mofosyne/openscad-rail-slot-mounts/screw/screw_mountable_smd_cut_tape_holder/png/screwMountableSMDcutTapeHolder.stl.png

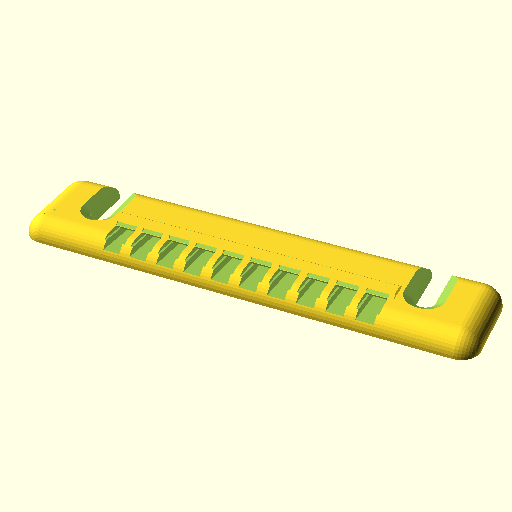
screw/screw_mountable_smd_cut_tape_holder/png/screwMountableSMDcutTapeHolder.stl.png
