mofosyne/openscad-rail-slot-mounts/screw/screw_mountable_wire_holder/png/screwMountableScrewdriverHolder.stl.png

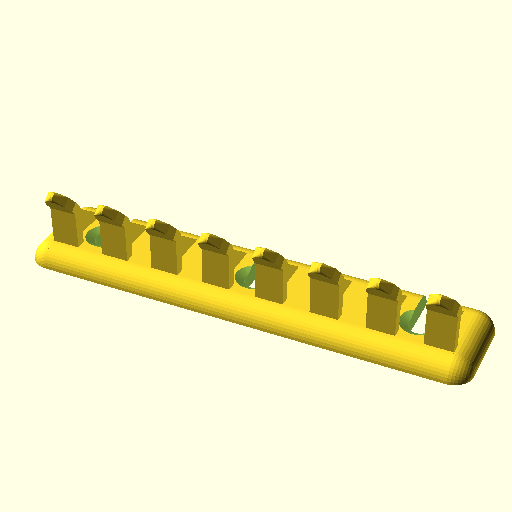
screw/screw_mountable_wire_holder/png/screwMountableScrewdriverHolder.stl.png
