mofosyne/openscad-rail-slot-mounts/screw/screw_mountable_wire_holder/png/screwMountableWireHolder.stl.png

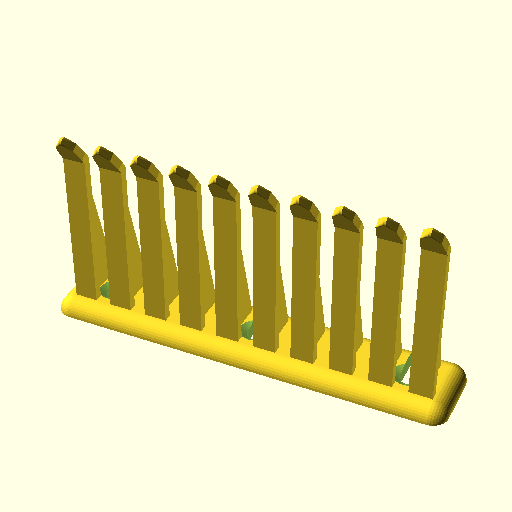
screw/screw_mountable_wire_holder/png/screwMountableWireHolder.stl.png
