mofosyne/openscad-rail-slot-mounts/tslot/png/tslot_cable_hook.stl.png

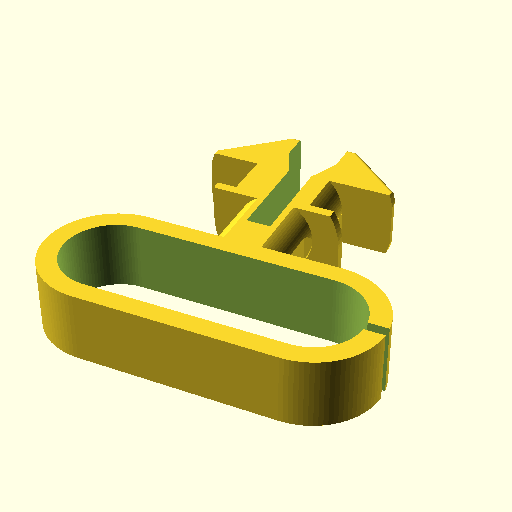
tslot/png/tslot_cable_hook.stl.png
