mofosyne/openscad-rail-slot-mounts/tslot/png/tslot_ethernet_cable_clip.stl.png

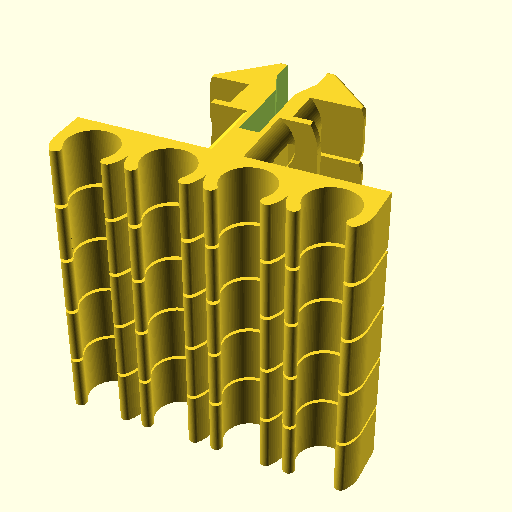
tslot/png/tslot_ethernet_cable_clip.stl.png
