mofosyne/openscad-rail-slot-mounts/tslot/png/tslot_screwdriver_mount.stl.png

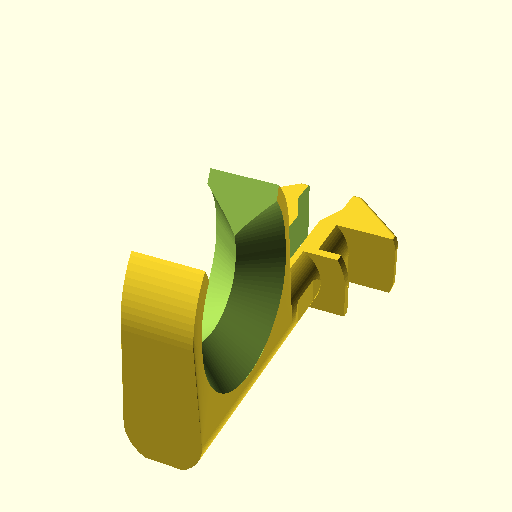
tslot/png/tslot_screwdriver_mount.stl.png
