mofosyne/openscad-rail-slot-mounts/tslot/png/tslot_tape_holderwCatch.stl.png

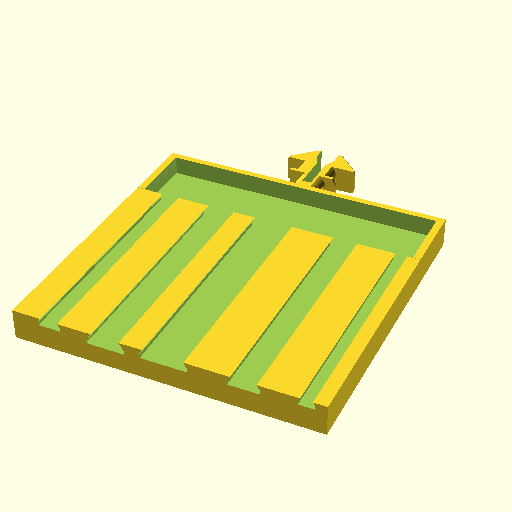
tslot/png/tslot_tape_holderwCatch.stl.png
