mofosyne/openscad-rail-slot-mounts/tslot/stl/tslot_pen_holder.stl

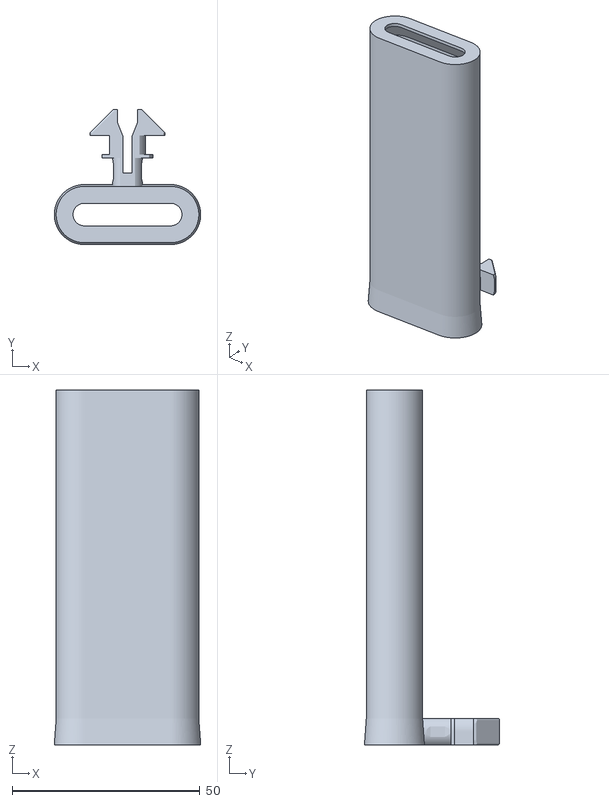
[picture p31: CAD file, 2024-09-13]
tslot/stl/tslot_pen_holder.stl
39.0 x 36.0 x 94.5
