mofosyne/openscad-rail-slot-mounts/tslot/stl/tslot.stl

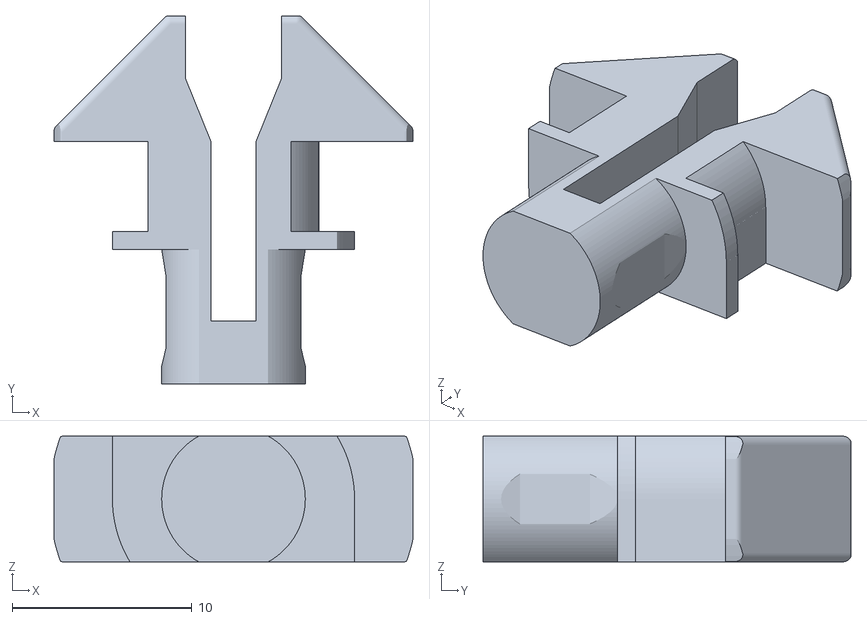
[picture p32: CAD file, 2024-09-13]
tslot/stl/tslot.stl
20.0 x 20.5 x 7.00
