mofosyne/openscad-rail-slot-mounts/tslot/stl/tslot_smd_feeder.stl

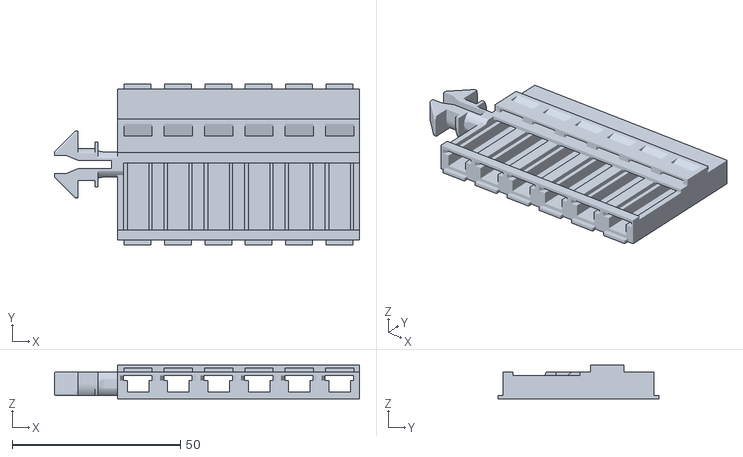
[picture p33: CAD file, 2024-09-13]
tslot/stl/tslot_smd_feeder.stl
90.8 x 48.0 x 10.0
