mofosyne/openscad-rail-slot-mounts/tslot/stl/tslot_cable_loop.stl

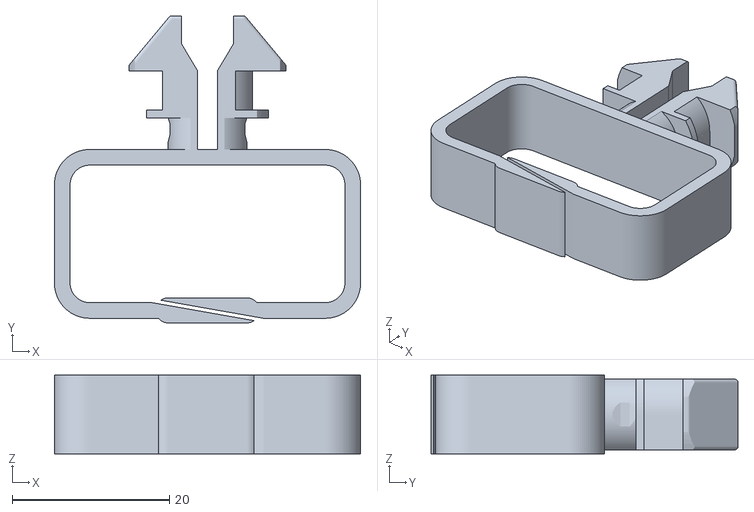
[picture p34: CAD file, 2024-09-13]
tslot/stl/tslot_cable_loop.stl
39.0 x 39.1 x 10.0
