mofosyne/openscad-rail-slot-mounts/tslot/stl/tslot_ethernet_cable_clip.stl

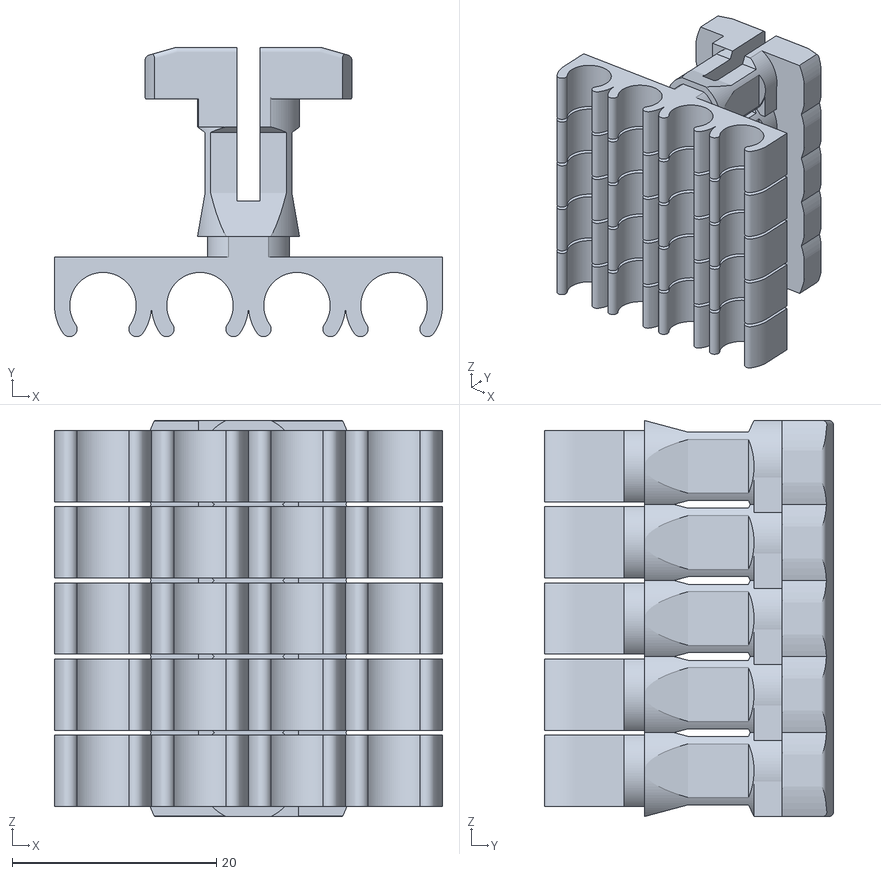
[picture p35: CAD file, 2024-09-08]
tslot/stl/tslot_ethernet_cable_clip.stl
38.0 x 28.3 x 38.8
