mofosyne/openscad-rail-slot-mounts/TRailExample.scad

rotate([90,0,0])
    linear_extrude(height = 100, center = true, scale=1.0)
        import(file = "TRailExample.svg", center = true, dpi = 96);
